MikhaelKaa/ZX_RS232_16550/FW_experiments/src/z80_ports.h

// Набор вспомогательных процедур для отладки и ресерча железа.
// Kargapolcev M. E.
// 15.07.2025

#ifndef _Z80_PORTS_
#define _Z80_PORTS_

// uCMD handler for mem_dump.
int ucmd_port(int argc, char **argv);

#endif /* _Z80_PORTS_ */
